josejacomeb/tinypico-cycling-tracker/code/arduino-tct/graphics.hpp

#pragma once
#include <Adafruit_GFX.h>

#define logo_width  121
#define logo_height 19

const uint8_t PROGMEM logo_data[] = {
  0b00001001,0b01000000,0b10000000,0b00000000,0b01100000,0b00000000,0b00000000,0b00000000,0b00000000,0b00000000,0b00000000,0b00000000,0b00000000,0b00000000,0b00000000,0b00000000,
  0b11111011,0b11111111,0b11100011,0b11111111,0b01000000,0b00000000,0b00000000,0b00000000,0b00000000,0b00000000,0b00000000,0b00000000,0b00000000,0b00000000,0b00000000,0b00000000,
  0b11101001,0b01011111,0b11100010,0b01011111,0b11000000,0b00000000,0b00000000,0b00000000,0b00000000,0b00000000,0b00000000,0b00000000,0b00000000,0b00000000,0b00000000,0b00000000,
  0b11111101,0b11011111,0b11101011,0b11111111,0b10000000,0b00000000,0b00000000,0b00000000,0b00000000,0b00000000,0b00000000,0b00000000,0b00000000,0b00000000,0b00000000,0b00000000,
  0b11100000,0b00000000,0b00000000,0b00000000,0b00000000,0b00000000,0b00000000,0b00000000,0b00000000,0b00000000,0b00000000,0b00000000,0b00000000,0b00000000,0b00000000,0b00000000,
  0b11001111,0b00001111,0b11000000,0b11111100,0b01111111,0b11000000,0b01111000,0b00111100,0b00000111,0b11110001,0b11111000,0b11111011,0b11101111,0b11111000,0b11111110,0b00000000,
  0b00001111,0b00011111,0b11100011,0b11111110,0b01111111,0b11000000,0b01111000,0b01111100,0b00001111,0b11110011,0b11111110,0b11111011,0b11101111,0b11111000,0b11111111,0b00000000,
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
  0b00000000,0b00001111,0b11011111,0b11100111,0b11000000,0b00000001,0b11111111,0b11111110,0b00000000,0b00000000,0b00000000,0b00000000,0b00000000,0b00000000,0b00000000,0b00000000,
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
};
