josejacomeb/tinypico-cycling-tracker/code/arduino-tct/workout.cpp

#include "workout.hpp"

// ---- Timing Methods ----

void Workout::start() {
  start_workout_ms = millis();
  totalDist_m = 0;
}

void Workout::end() {
  total_ms = millis() - start_workout_ms;
}

void Workout::reset() {
  start_workout_ms = 0;
  elapsed_workout_ms = 0;
}

// ---- Distance Calculation Methods ----

double Workout::haversine(TinyGPSLocation& Pos1, TinyGPSLocation& Pos2) {
  const double R = 6371000.0;
  double dlat = (Pos2.lat() - Pos1.lat()) * DEG_TO_RAD;
  double dlon = (Pos2.lng() - Pos1.lng()) * DEG_TO_RAD;
  double a = sin(dlat / 2) * sin(dlat / 2) + cos(Pos1.lat() * DEG_TO_RAD) * cos(Pos2.lat() * DEG_TO_RAD) * sin(dlon / 2) * sin(dlon / 2);
  return R * 2 * atan2(sqrt(a), sqrt(1 - a));
}

// ---- Waypoint Management ----

void Workout::pushWP(TinyGPSLocation& Pos1, double alt) {
  WP wp = { Pos1, alt, 0.0, true };
  if (!win[win_end].valid) {
    win[win_end] = wp;
    win_end = (win_end + 1) % MAXW;
    return;
  }
  int prev = (win_end - 1 + MAXW) % MAXW;
  double d = haversine(win[prev].Pos, Pos1);
  wp.accumDist = win[prev].accumDist + d;
  win[win_end] = wp;
  win_end = (win_end + 1) % MAXW;

  while (true) {
    int s = win_start;
    int e = (win_end - 1 + MAXW) % MAXW;
    if (!win[s].valid || !win[e].valid) break;
    double wd = win[e].accumDist - win[s].accumDist;
    if (wd > GPS_GRADE_WINDOW) {
      win[s].valid = false;
      win_start = (win_start + 1) % MAXW;
    } else break;
  }
  elapsed_workout_ms = millis() - start_workout_ms;
  lastPos = { Pos1, alt, true };
}

// ---- Grade Calculation ----

bool Workout::gpsGrade(double& grade) {
  int s = win_start;
  int e = (win_end - 1 + MAXW) % MAXW;
  if (!win[s].valid || !win[e].valid) return false;
  if (s == e) return false;

  double hd = win[e].accumDist - win[s].accumDist;
  if (hd < 3.0) return false;

  double ed = win[e].alt - win[s].alt;
  grade = (ed / hd) * 100.0;
  return true;
}

// ---- Pace Calculation ----

char* Workout::paceFromSpeed(double speed_m_s) {
  if (speed_m_s < 0.5) {
    snprintf(buf, 6, "--:--");
    return buf;
  }
  double secpkm = 1000.0 / speed_m_s;
  int mm = int(secpkm / 60);
  int ss = int(secpkm - mm * 60);
  if (ss == 60) {
    mm++;
    ss = 0;
  }
  sprintf(buf, "%02d:%02d", mm, ss);
  return buf;
}

// ---- Slope Calculation ----

double& Workout::get_slope(float& pitch) {
  double ggrade = 0;
  float imuSlopePercent = tan(pitch * DEG_TO_RAD) * 100.0;
  if (gpsGrade(ggrade)) {
    slope = ALPHA_IMU * imuSlopePercent + (1.0 - ALPHA_IMU) * ggrade;
  }
  return slope;
}

// ---- Getters/Setters ----

void Workout::add_distance(double distance) {
  totalDist_m += distance;
}

double& Workout::get_total_distance() {
  return totalDist_m;
}

unsigned long& Workout::get_total_ms() {
  return total_ms;
}

unsigned long& Workout::get_elapsed_workout_time() {
  elapsed_workout_ms = millis() - start_workout_ms;
  return elapsed_workout_ms;
}

TinyGPSLocation& Workout::get_last_location() {
  return lastPos.Pos;
}

bool Workout::is_last_pos_valid() {
  return lastPos.valid;
}
