josejacomeb/tinypico-cycling-tracker/code/arduino-tct/matrix.cpp

 
/************************************************************************************
 * Class Matrix
 *  See matrix.h for description
 * 
 * See https://github.com/pronenewbits for more!
 *************************************************************************************/

#include <Arduino.h>
#include "matrix.h"

/* There's nothing here yet! */
